Archive-663/jericho941/CowboyBebopGrips/STEP/jericho941_pre2007_grip_cowboyBebop_laserCover_batteryPositiveLead_10mm.stp

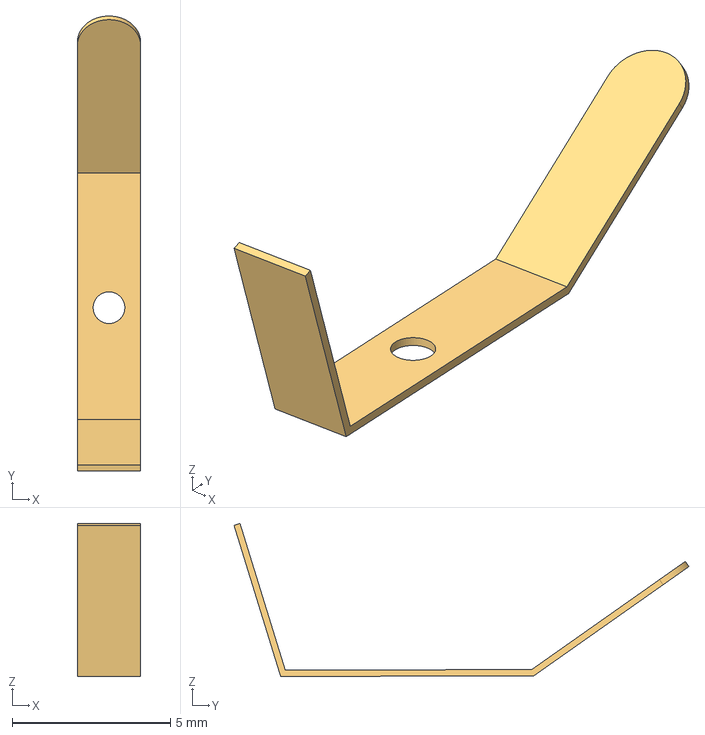
[picture p32: CAD file, 2024-08-04]
CowboyBebopGrips/STEP/jericho941_pre2007_grip_cowboyBebop_laserCover_batteryPositiveLead_10mm.stp
2.00 x 14.4 x 4.84 mm
