Archive-663/jericho941/Stand/STEP/jericho941_pre2007_standCoin_bebop.stp

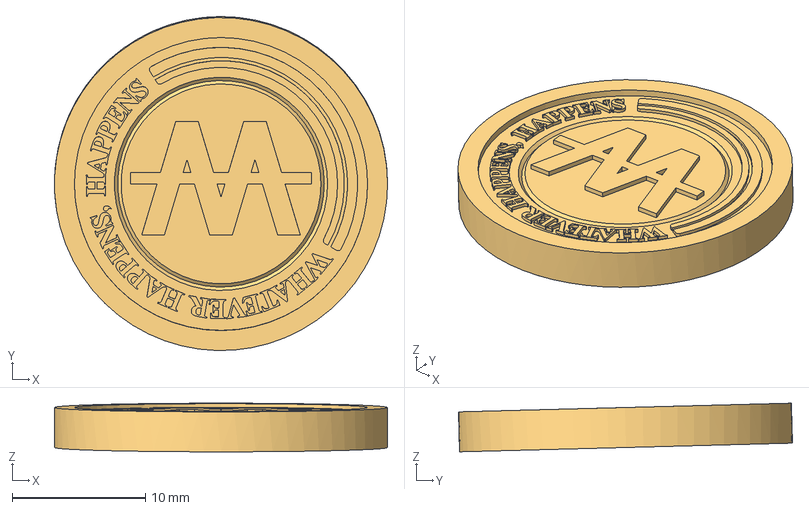
[picture p33: CAD file, 2024-02-22]
Stand/STEP/jericho941_pre2007_standCoin_bebop.stp
25.0 x 25.1 x 3.65 mm
