Archive-663/jericho941/CowboyBebopGrips/STEP/jericho941_pre2007_grip_cowboyBebop_laserCover_batteryDoor_10mm.stp

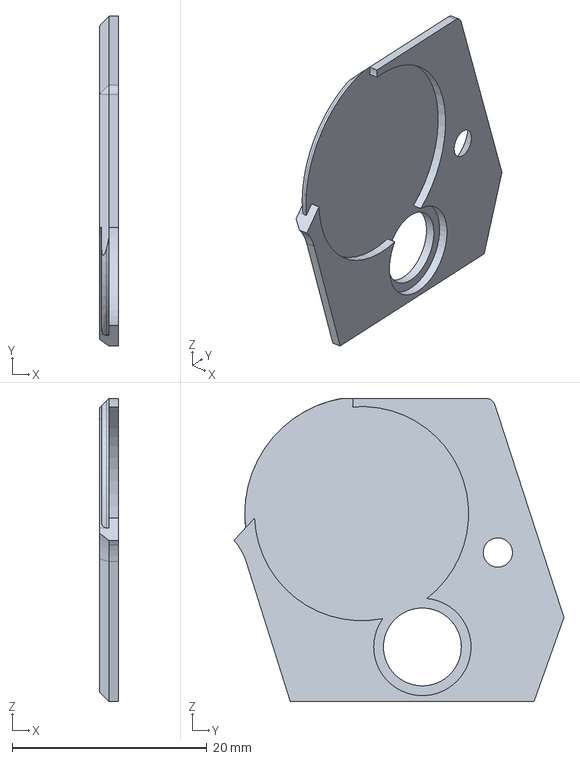
[picture p34: CAD file, 2024-08-04]
CowboyBebopGrips/STEP/jericho941_pre2007_grip_cowboyBebop_laserCover_batteryDoor_10mm.stp
2.00 x 33.9 x 31.2 mm
