Archive-663/jericho941/CowboyBebopGrips/STEP/jericho941_pre2007_grip_cowboyBebop_laserCover_batteryNegativeLead_10mm.stp

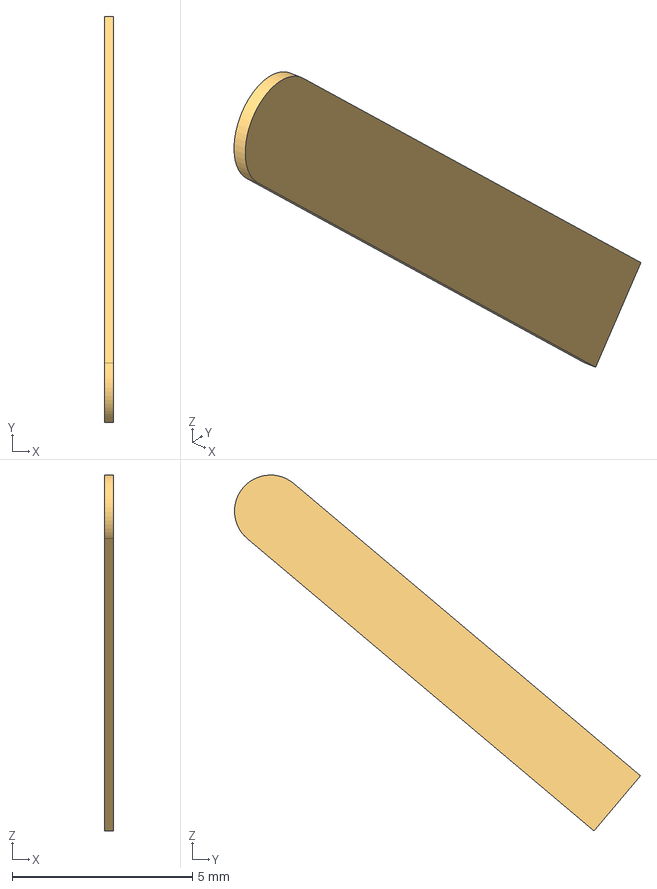
[picture p35: CAD file, 2024-08-04]
CowboyBebopGrips/STEP/jericho941_pre2007_grip_cowboyBebop_laserCover_batteryNegativeLead_10mm.stp
0.25 x 11.3 x 9.87 mm
