Archive-663/jericho941/CowboyBebopGrips/STEP/jericho941_pre2007_grip_cowboyBebop_laserCover_plugTPU_10mm.stp

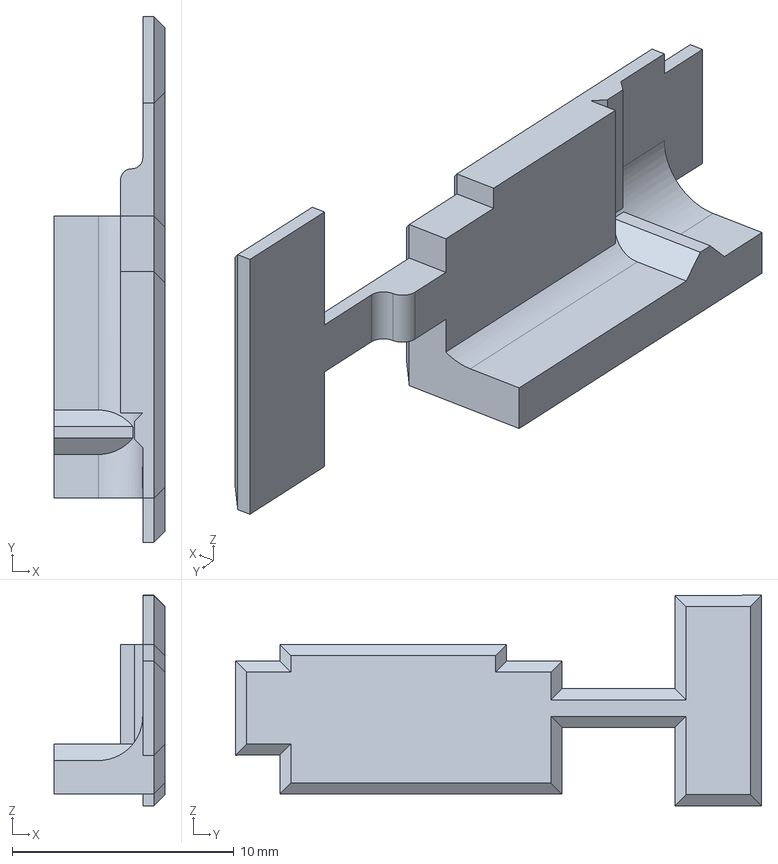
[picture p36: CAD file, 2024-08-04]
CowboyBebopGrips/STEP/jericho941_pre2007_grip_cowboyBebop_laserCover_plugTPU_10mm.stp
5.00 x 23.7 x 9.49 mm
