Archive-663/jericho941/CowboyBebopGrips/STEP/jericho941_pre2007_grip_cowboyBebop_frontStrap.stp

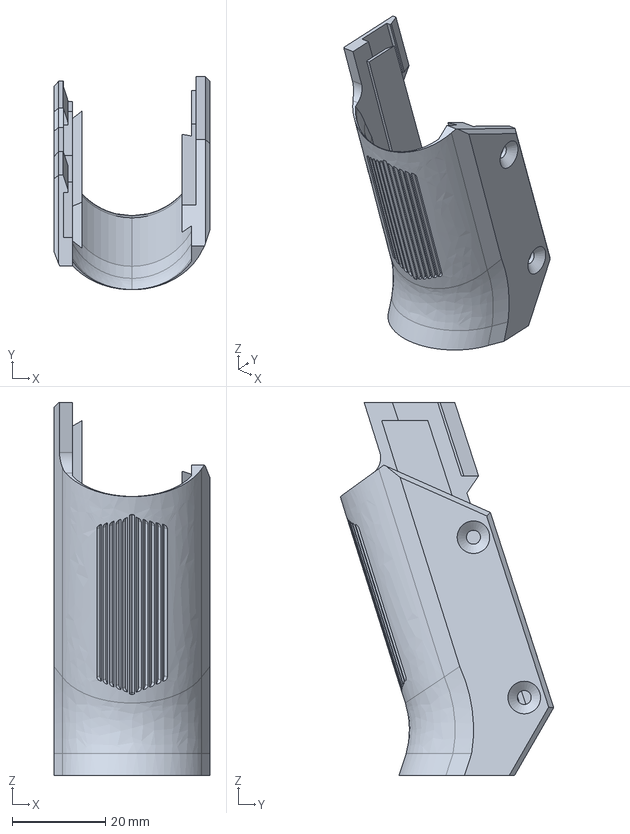
[picture p37: CAD file, 2024-08-04]
CowboyBebopGrips/STEP/jericho941_pre2007_grip_cowboyBebop_frontStrap.stp
33.5 x 45.9 x 80.2 mm
