Archive-663/jericho941/CowboyBebopGrips/STEP/jericho941_pre2007_grip_cowboyBebop_laserCover_buttonTPU_10mm.stp

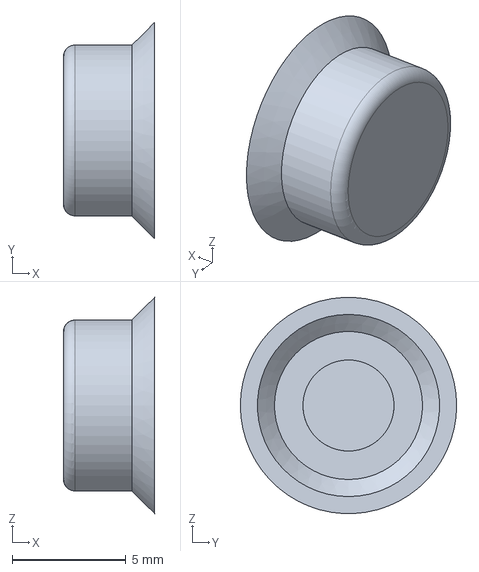
[picture p38: CAD file, 2024-08-04]
CowboyBebopGrips/STEP/jericho941_pre2007_grip_cowboyBebop_laserCover_buttonTPU_10mm.stp
4.00 x 9.50 x 9.49 mm
