Archive-663/jericho941/CowboyBebopGrips/STEP/jericho941_pre2007_grip_cowboyBebop_laserPlate_forCNC.stp

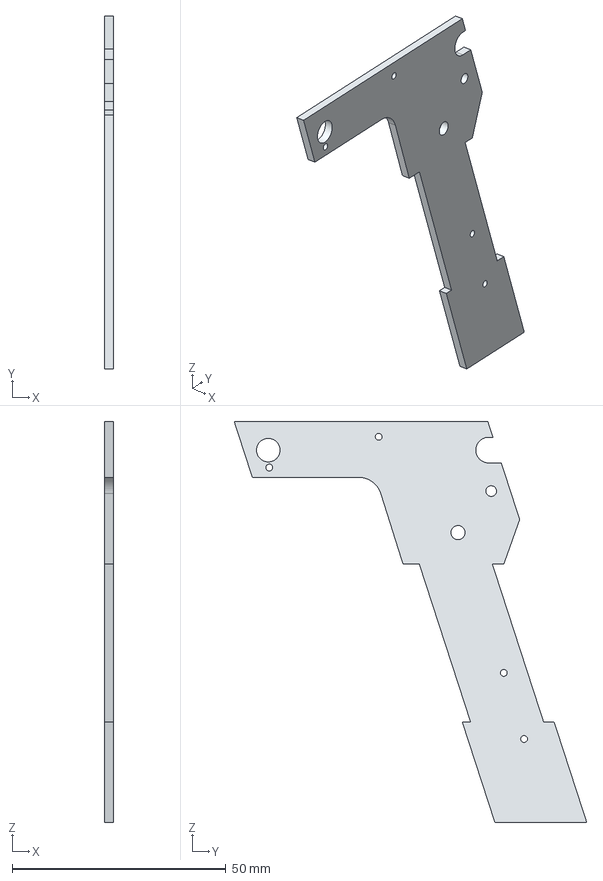
[picture p39: CAD file, 2024-08-04]
CowboyBebopGrips/STEP/jericho941_pre2007_grip_cowboyBebop_laserPlate_forCNC.stp
2.00 x 82.4 x 93.7 mm
